Alx3dp/Bondtech-INDX-Monolith-gantry-integration/4 - Tool bars/4.1 awd/Printed parts/Monolith INDX awd tool bar mount left.stl

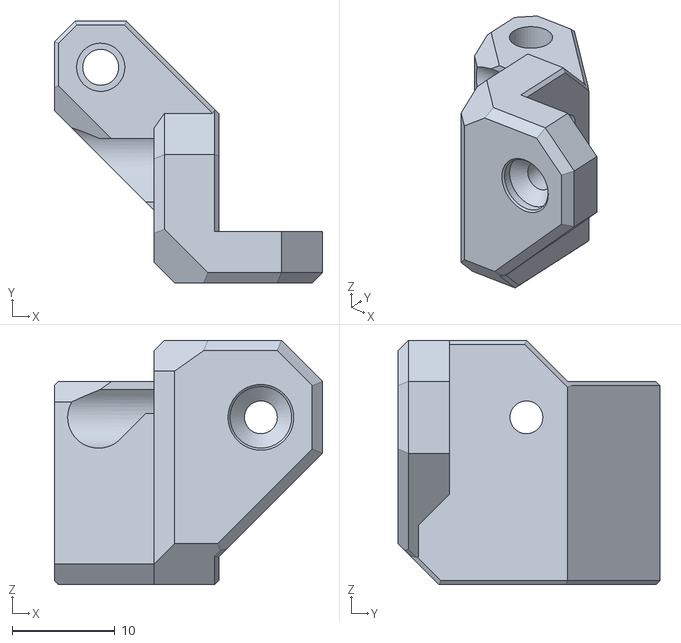
[picture p15: CAD file, 2026-07-06]
4 - Tool bars/4.1 awd/Printed parts/Monolith INDX awd tool bar mount left.stl
26.1 x 25.5 x 23.8
