Alx3dp/Bondtech-INDX-Monolith-gantry-integration/4 - Tool bars/4.2 2wd for printed/6mm belts/fixed gantry/CAD/Monolith INDX Toolbar 250mm 2WD 6mm fixed gantry.step

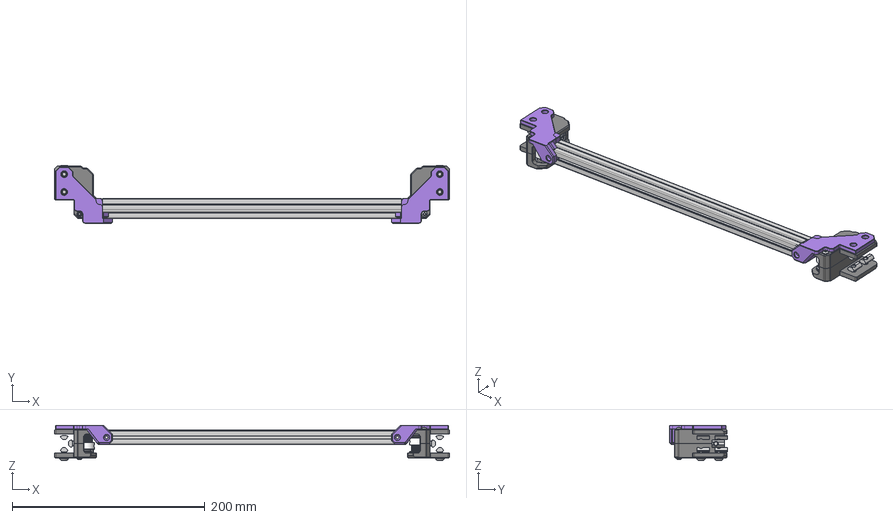
[picture p16: CAD file, 2026-07-06]
4 - Tool bars/4.2 2wd for printed/6mm belts/fixed gantry/CAD/Monolith INDX Toolbar 250mm 2WD 6mm fixed gantry.step
410.0 x 59.8 x 36.8 mm
Printed_VT_6mm_front_motorless_mount_a x 2
Printed_VT_6mm_front_motorless_mount_b x 2
GT2 20T 6mm pulley x 2
F695 flanged bearing x 8
Shim 1mm x 2
Shim 0.5mm x 6
D5x30 smooth pin x 4
Printed_spacer x 2
M3x30 BHCS x 2
M3xD5x4 threaded insert x 2
M5x16 BHCS x 2
M5 washer x 2
M5 2020 drop-in T-nut x 10
M5x10 BHCS x 4
