Alx3dp/Bondtech-INDX-Monolith-gantry-integration/4 - Tool bars/4.2 2wd for printed/6mm belts/fixed gantry/printed parts/FT/FT Toolbar connector left.stl

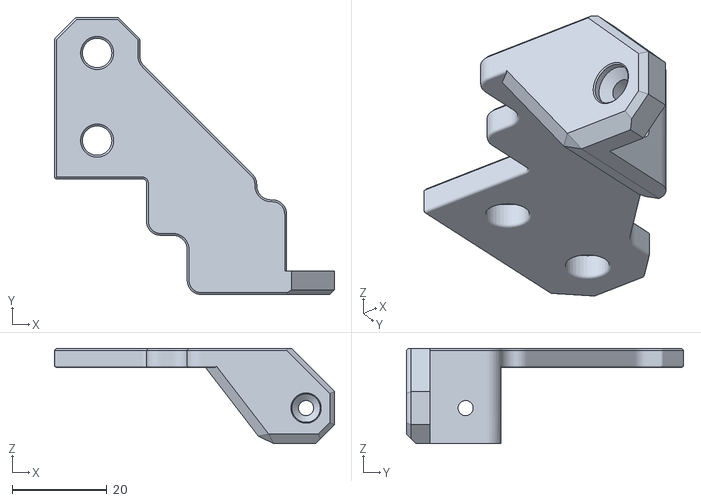
[picture p17: CAD file, 2026-07-06]
4 - Tool bars/4.2 2wd for printed/6mm belts/fixed gantry/printed parts/FT/FT Toolbar connector left.stl
59.1 x 58.5 x 20.1
