Alx3dp/Bondtech-INDX-Monolith-gantry-integration/4 - Tool bars/4.2 2wd for printed/9mm belts/fixed gantry/printed parts/NP/NP Toolbar connector right.stl

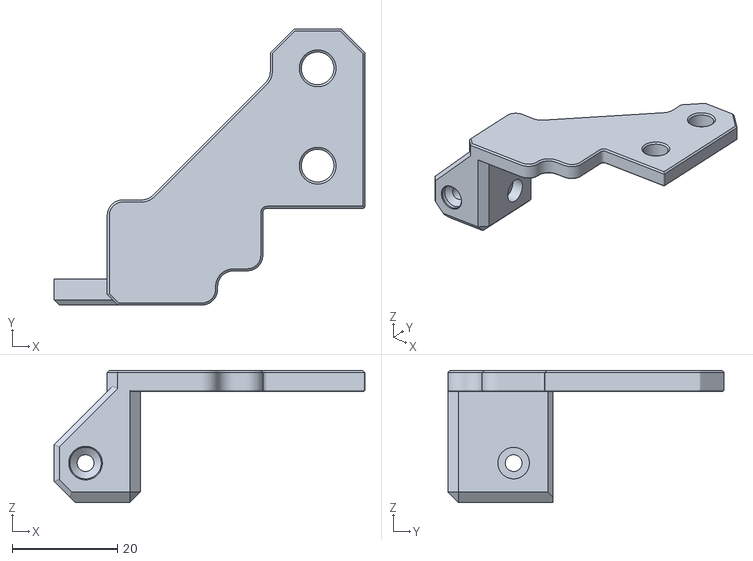
[picture p24: CAD file, 2026-07-06]
4 - Tool bars/4.2 2wd for printed/9mm belts/fixed gantry/printed parts/NP/NP Toolbar connector right.stl
59.1 x 52.5 x 25.1
