Alx3dp/Bondtech-INDX-Monolith-gantry-integration/4 - Tool bars/4.2 2wd for printed/9mm belts/flying gantry/printed parts/modified Z joint left.stl

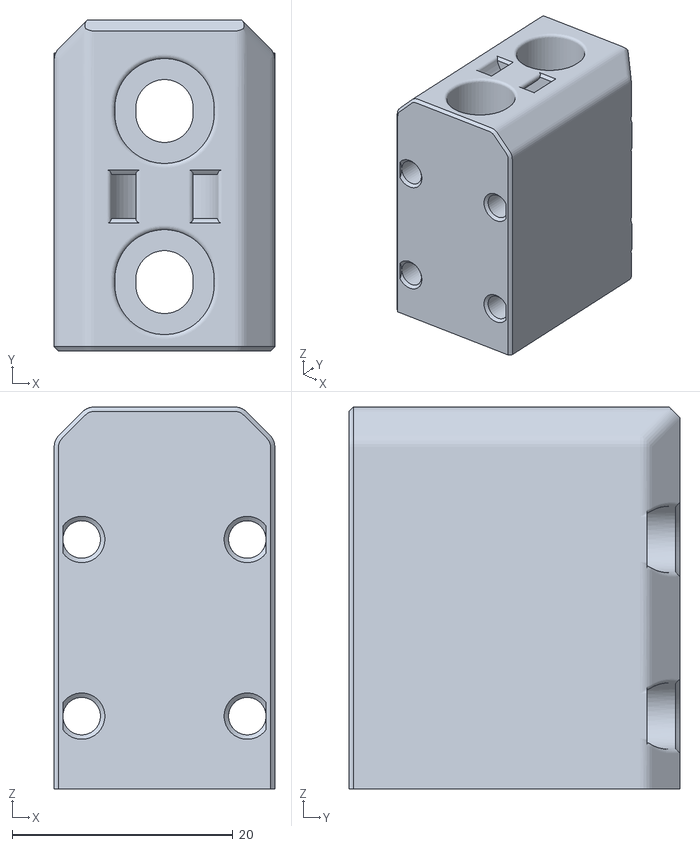
[picture p27: CAD file, 2026-07-06]
4 - Tool bars/4.2 2wd for printed/9mm belts/flying gantry/printed parts/modified Z joint left.stl
20.0 x 30.0 x 34.6
