Alx3dp/Bondtech-INDX-Monolith-gantry-integration/4 - Tool bars/4.2 2wd for printed/9mm belts/flying gantry/printed parts/NP/NP Toolbar connector right.stl

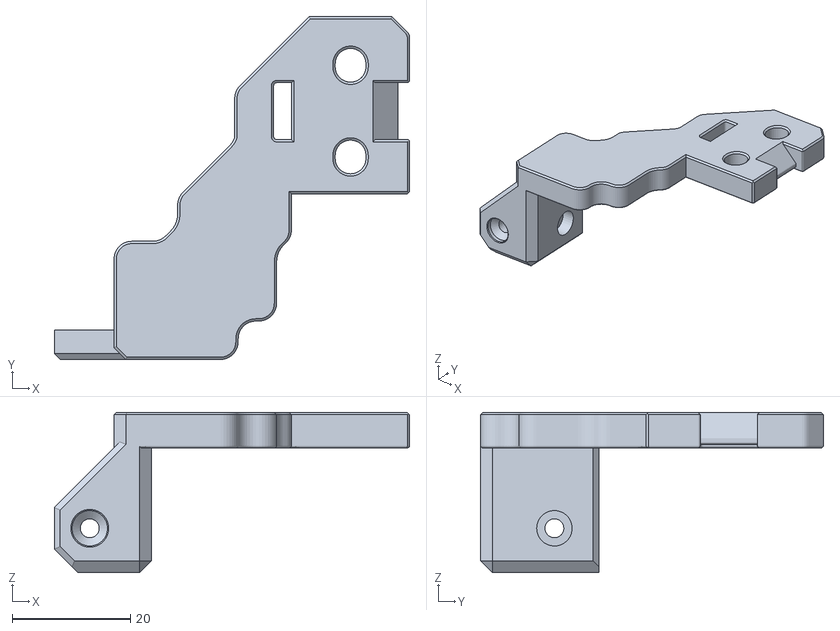
[picture p28: CAD file, 2026-07-06]
4 - Tool bars/4.2 2wd for printed/9mm belts/flying gantry/printed parts/NP/NP Toolbar connector right.stl
60.1 x 58.0 x 27.1
