Alx3dp/Bondtech-INDX-Monolith-gantry-integration/5 - Miscellaneous/motor cover with nozzle cam pcb mount/motor cover.step

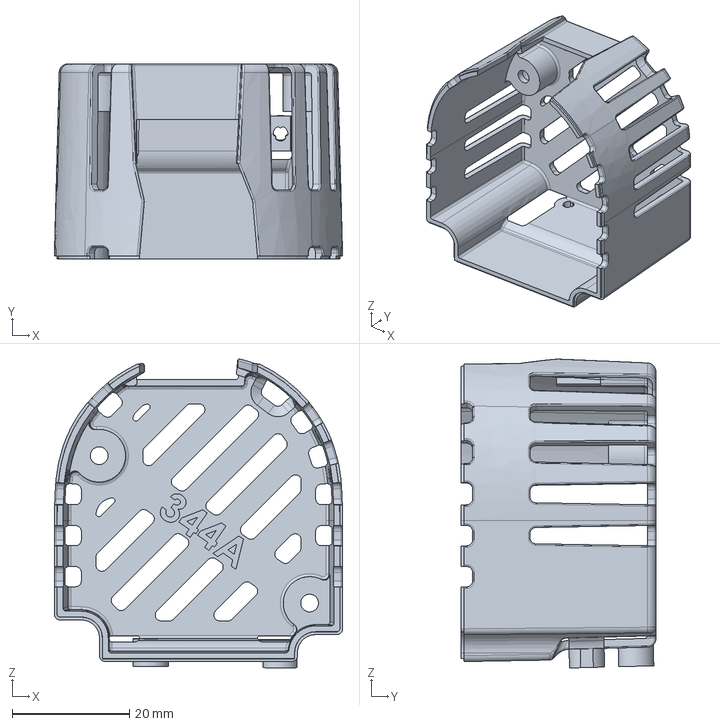
[picture p29: CAD file, 2026-07-02]
5 - Miscellaneous/motor cover with nozzle cam pcb mount/motor cover.step
49.2 x 33.3 x 52.7 mm
