Alx3dp/Bondtech-INDX-Monolith-gantry-integration/1 - Belt clamp/1.1 - without nozzle cam compatibility/Printed parts/belt clamp plate.stl

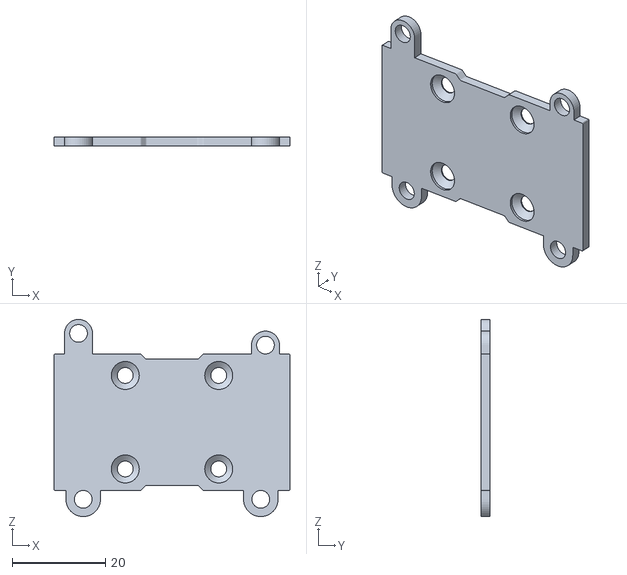
[picture p30: CAD file, 2026-07-02]
1 - Belt clamp/1.1 - without nozzle cam compatibility/Printed parts/belt clamp plate.stl
50.5 x 2.00 x 42.2
