Alx3dp/Bondtech-INDX-Monolith-gantry-integration/1 - Belt clamp/1.2 - with nozzle cam compatibility/printed parts/belt clamp with nozzle cam.stl

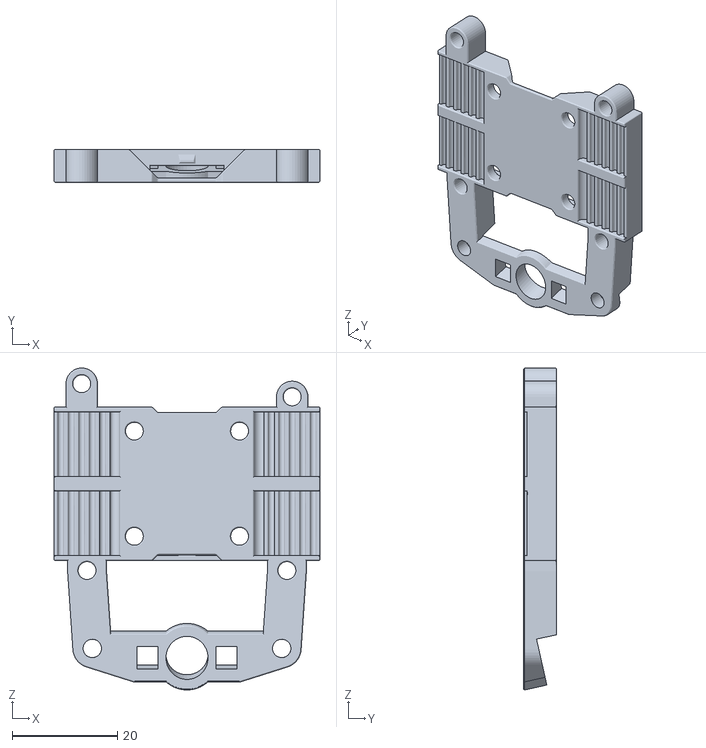
[picture p31: CAD file, 2026-07-02]
1 - Belt clamp/1.2 - with nozzle cam compatibility/printed parts/belt clamp with nozzle cam.stl
50.5 x 6.24 x 61.2
