Alx3dp/Bondtech-INDX-Monolith-gantry-integration/4 - Tool bars/4.0 toolholder/printed parts/Toolholder.stl

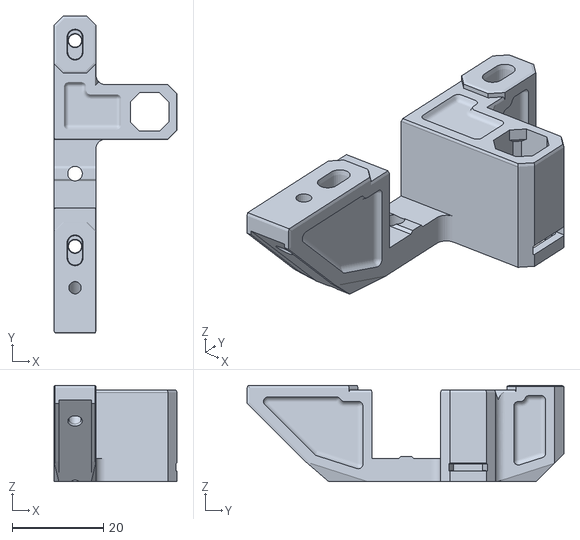
[picture p32: CAD file, 2026-07-04]
4 - Tool bars/4.0 toolholder/printed parts/Toolholder.stl
26.9 x 69.3 x 21.0
