Alx3dp/Bondtech-INDX-Monolith-gantry-integration/4 - Tool bars/4.1 awd/CAD/flying gantry/9mm/Monolith INDX Toolbar 300mm AWD 9mm flying gantry.step

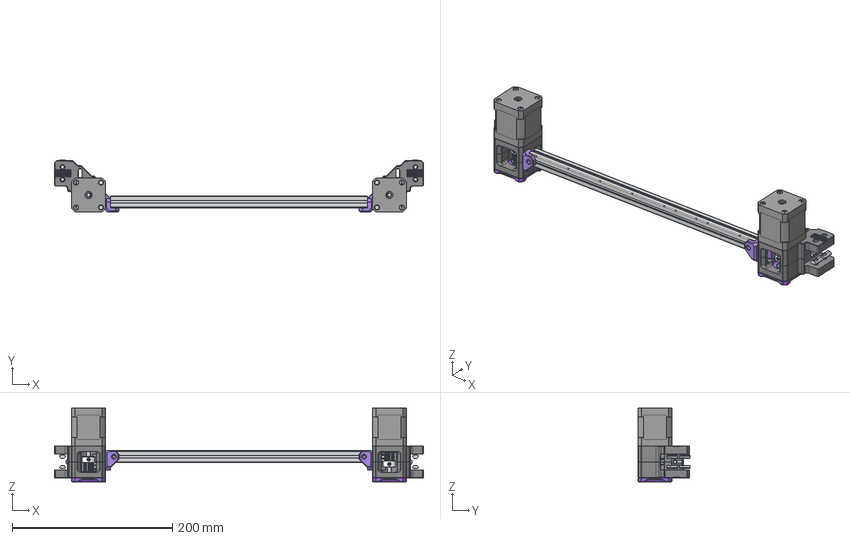
[picture p33: CAD file, 2026-07-06]
4 - Tool bars/4.1 awd/CAD/flying gantry/9mm/Monolith INDX Toolbar 300mm AWD 9mm flying gantry.step
460.0 x 64.6 x 92.0 mm
Printed_V2_9mm_front_motor_mount_a x 2
Printed_V2_9mm_front_motor_mount_b x 2
GT2 20T 9mm pulley x 2
F695 flanged bearing x 6
Shim 0.5mm x 8
695 bearing x 2
D5x40 smooth pin x 2
M5 2020 drop-in T-nut x 10
M5x10 BHCS x 2
M5 washer x 2
Printed_long_shaft_double_shear_twist_lock x 2
M3x45 SHCS x 8
M3 washer x 8
Printed_long_shaft_double_shear_housing x 2
_S45R shaft x 2
_stepper x 2
