Alx3dp/Bondtech-INDX-Monolith-gantry-integration/4 - Tool bars/4.0 toolholder/printed parts/magnet spring holder.stl

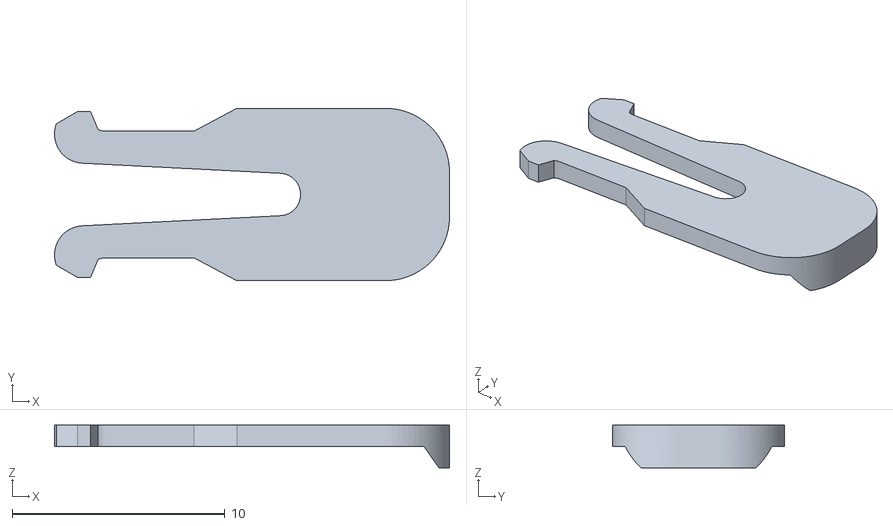
[picture p34: CAD file, 2026-07-04]
4 - Tool bars/4.0 toolholder/printed parts/magnet spring holder.stl
18.6 x 8.10 x 2.00
